Chittesh195/Circuit-and-Communication-Laboratory/LTspice/FINAL_CIRCUIT.asc

C1: cap; 0.1µ
R1: res; 4.7k
R2: res; 4.7k
R3: res; 1k
U1: LM741
U2: LM741
V1: voltage; 12
V2: voltage; 12
V3: voltage; 12
V4: voltage; 12
Named nets: 0, Square_output, Triangle_Output
.tran 5m
Stage 1
Stage 2
